taaki2311/LabPowerSupply/Plots/current_plot.png

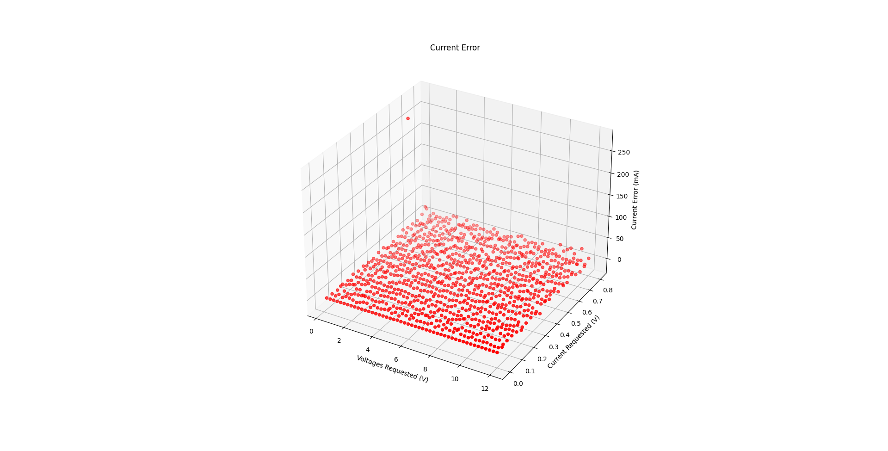
Plots/current_plot.png
